milestogo/ergo_reform/reform2-keyboard-pcb/reform2-keyboard-backlight.kicad_sch

## KiCad design reform2-keyboard-pcb/reform2-keyboard-backlight.kicad_sch (2022-06-05)

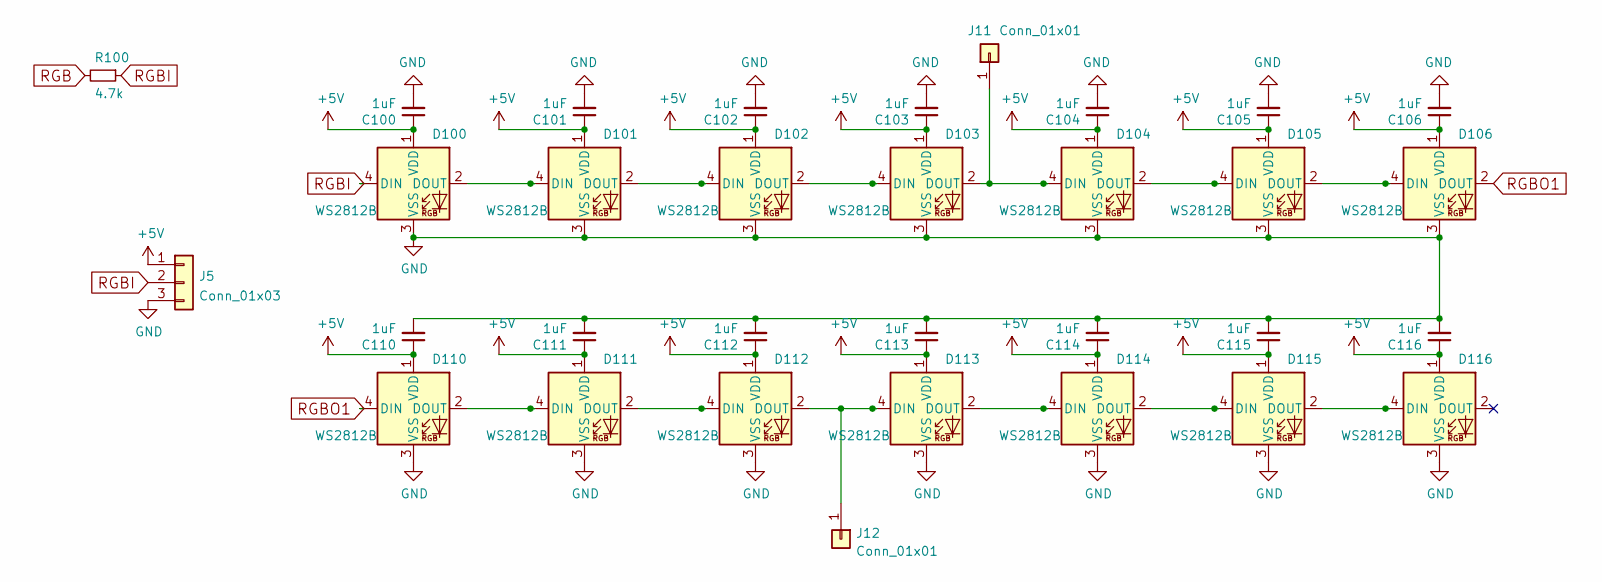
[picture p25: schematic reform2-keyboard-backlight.kicad_sch]

Parts:
C100, C101, C102, C103, C104, C105, C106, C110, C111, C112, C113, C114, C115, C116: 1uF; C_0805_2012Metric_Pad1.18x1.45mm_HandSolder
D100, D101, D102, D103, D104, D105, D106, D110, D111, D112, D113, D114, D115, D116: WS2812B; SK6812-MINI-E
J5: Conn_01x03; PinHeader_1x03_P2.54mm_Vertical
J11, J12: Conn_01x01; PinHeader_1x01_P2.00mm_Vertical
R100: 4.7k; R_0805_2012Metric_Pad1.20x1.40mm_HandSolder

Connections:
+5V: C100.1, C101.1, C102.1, C103.1, C104.1, C105.1, C106.1, C110.1, C111.1, C112.1, C113.1, C114.1, C115.1, C116.1, D100.1 (VDD), D101.1 (VDD), D102.1 (VDD), D103.1 (VDD), D104.1 (VDD), D105.1 (VDD), D106.1 (VDD), D110.1 (VDD), D111.1 (VDD), D112.1 (VDD), D113.1 (VDD), D114.1 (VDD), D115.1 (VDD), D116.1 (VDD), J5.1
GND: C100.2, C101.2, C102.2, C103.2, C104.2, C105.2, C106.2, C110.2, C111.2, C112.2, C113.2, C114.2, C115.2, C116.2, D100.3 (VSS), D101.3 (VSS), D102.3 (VSS), D103.3 (VSS), D104.3 (VSS), D105.3 (VSS), D106.3 (VSS), D110.3 (VSS), D111.3 (VSS), D112.3 (VSS), D113.3 (VSS), D114.3 (VSS), D115.3 (VSS), D116.3 (VSS), J5.3
unnamed: D100.2 (DOUT), D101.4 (DIN)
unnamed: D101.2 (DOUT), D102.4 (DIN)
unnamed: D102.2 (DOUT), D103.4 (DIN)
unnamed: D103.2 (DOUT), D104.4 (DIN), J11.1
unnamed: D104.2 (DOUT), D105.4 (DIN)
unnamed: D105.2 (DOUT), D106.4 (DIN)
unnamed: D110.2 (DOUT), D111.4 (DIN)
unnamed: D111.2 (DOUT), D112.4 (DIN)
unnamed: D112.2 (DOUT), D113.4 (DIN), J12.1
unnamed: D113.2 (DOUT), D114.4 (DIN)
unnamed: D114.2 (DOUT), D115.4 (DIN)
unnamed: D115.2 (DOUT), D116.4 (DIN)
RGB: R100.2
RGBI: D100.4 (DIN), J5.2, R100.1
RGBO1: D106.2 (DOUT), D110.4 (DIN)
