milestogo/ergo_reform/reform2-keyboard-pcb/reform2-keyboard.kicad_sch

## KiCad design reform2-keyboard-pcb/reform2-keyboard.kicad_sch (2022-06-05)

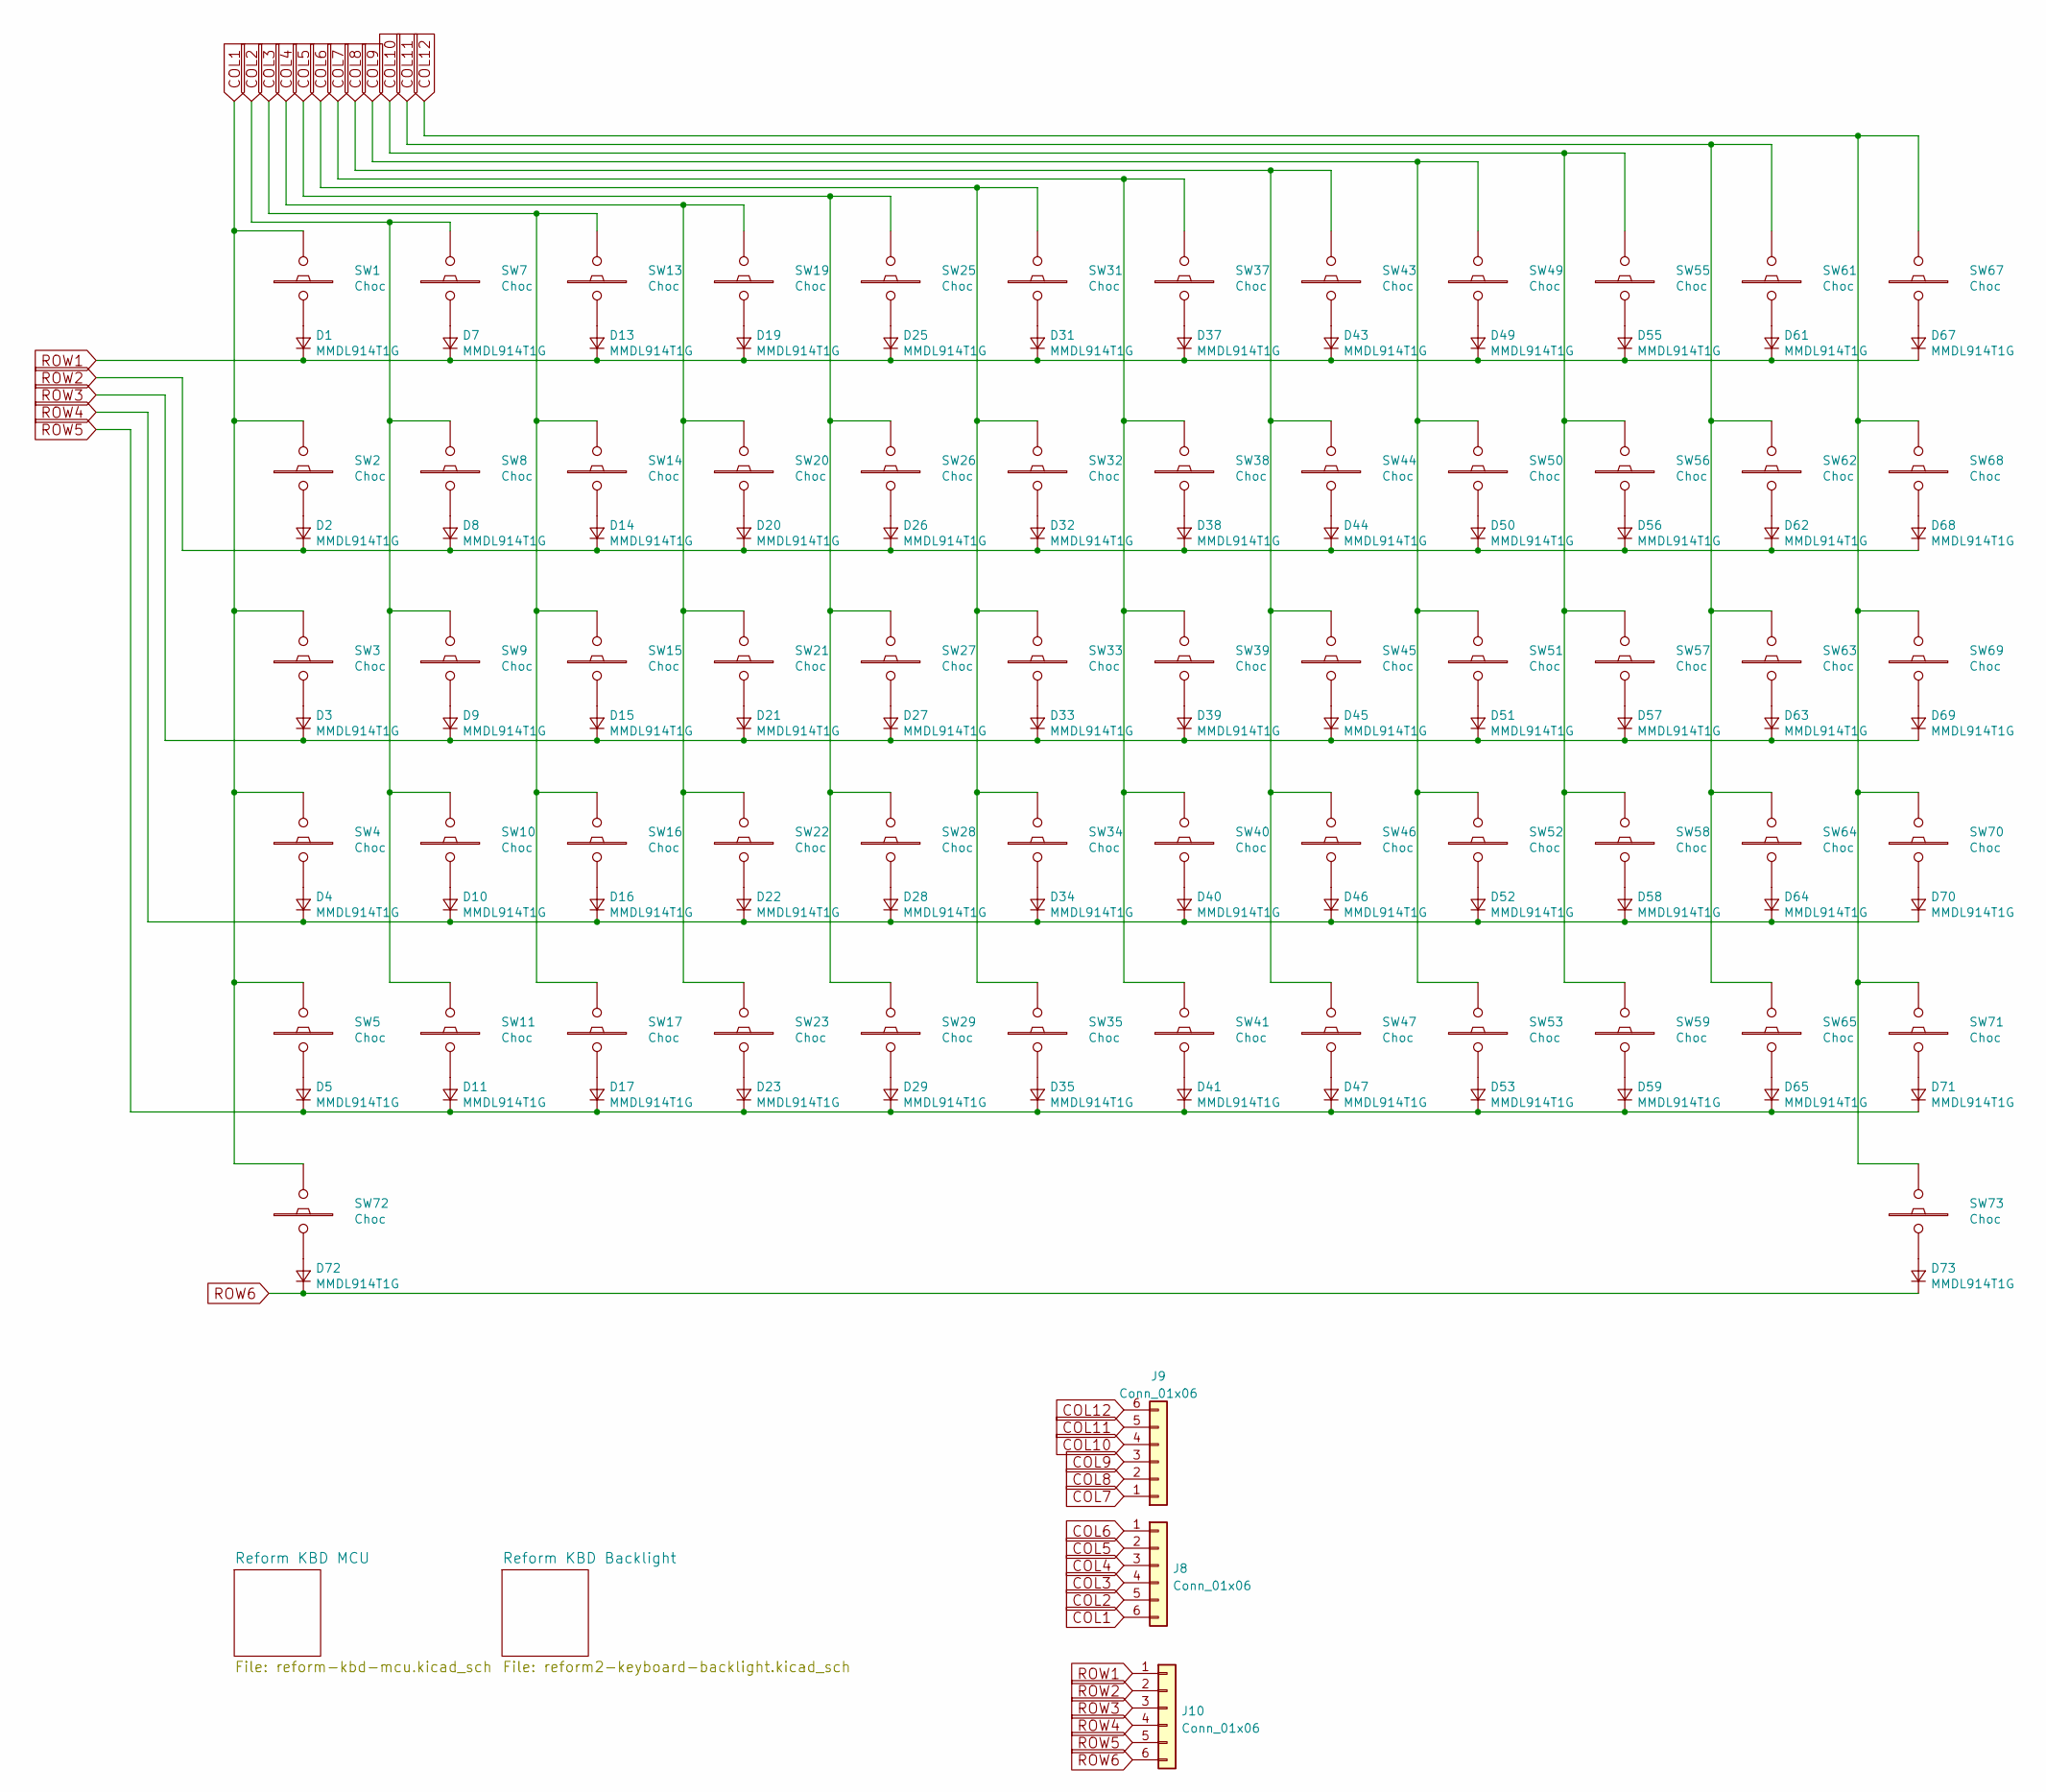
[picture p26: schematic reform2-keyboard.kicad_sch]

Parts:
D1, D2, D3, D4, D5, D7, D8, D9, D10, D11, D13, D14, D15, D16, D17, D19, D20, D21, D22, D23, D25, D26, D27, D28, D29, D31, D32, D33, D34, D35, D37, D38, D39, D40, D41, D43, D44, D45, D46, D47, D49, D50, D51, D52, D53, D55, D56, D57, D58, D59, D61, D62, D63, D64, D65, D67, D68, D69, D70, D71, D72, D73: MMDL914T1G; D_SOD-123
J8, J9, J10: Conn_01x06; PinHeader_1x06_P2.54mm_Vertical
SW1, SW7, SW13, SW27, SW29, SW35, SW41, SW45, SW47, SW55, SW61, SW67, SW72, SW73: Choc; PG1350
SW2, SW3, SW4, SW5, SW8, SW9, SW10, SW11, SW14, SW15, SW16, SW17, SW19, SW20, SW21, SW22, SW23, SW25, SW26, SW28, SW31, SW32, SW33, SW34, SW37, SW38, SW39, SW40, SW43, SW44, SW46, SW49, SW50, SW51, SW52, SW53, SW56, SW57, SW58, SW59, SW62, SW63, SW64, SW65, SW68, SW69, SW70, SW71: Choc; PG1350_optional-socket

Connections:
COL1: J8.6, SW1.1, SW2.1, SW3.1, SW4.1, SW5.1, SW72.1
COL2: J8.5, SW7.1, SW8.1, SW9.1, SW10.1, SW11.1
COL3: J8.4, SW13.1, SW14.1, SW15.1, SW16.1, SW17.1
COL4: J8.3, SW19.1, SW20.1, SW21.1, SW22.1, SW23.1
COL5: J8.2, SW25.1, SW26.1, SW27.1, SW28.1, SW29.1
COL6: J8.1, SW31.1, SW32.1, SW33.1, SW34.1, SW35.1
COL7: J9.1, SW37.1, SW38.1, SW39.1, SW40.1, SW41.1
COL8: J9.2, SW43.1, SW44.1, SW45.1, SW46.1, SW47.1
COL9: J9.3, SW49.1, SW50.1, SW51.1, SW52.1, SW53.1
COL10: J9.4, SW55.1, SW56.1, SW57.1, SW58.1, SW59.1
COL11: J9.5, SW61.1, SW62.1, SW63.1, SW64.1, SW65.1
COL12: J9.6, SW67.1, SW68.1, SW69.1, SW70.1, SW71.1, SW73.1
unnamed: D1.2 (A), SW1.2
unnamed: D2.2 (A), SW2.2
unnamed: D3.2 (A), SW3.2
unnamed: D4.2 (A), SW4.2
unnamed: D5.2 (A), SW5.2
unnamed: D7.2 (A), SW7.2
unnamed: D8.2 (A), SW8.2
unnamed: D9.2 (A), SW9.2
unnamed: D10.2 (A), SW10.2
unnamed: D11.2 (A), SW11.2
unnamed: D13.2 (A), SW13.2
unnamed: D14.2 (A), SW14.2
unnamed: D15.2 (A), SW15.2
unnamed: D16.2 (A), SW16.2
unnamed: D17.2 (A), SW17.2
unnamed: D19.2 (A), SW19.2
unnamed: D20.2 (A), SW20.2
unnamed: D21.2 (A), SW21.2
unnamed: D22.2 (A), SW22.2
unnamed: D23.2 (A), SW23.2
unnamed: D25.2 (A), SW25.2
unnamed: D26.2 (A), SW26.2
unnamed: D27.2 (A), SW27.2
unnamed: D28.2 (A), SW28.2
unnamed: D29.2 (A), SW29.2
unnamed: D31.2 (A), SW31.2
unnamed: D32.2 (A), SW32.2
unnamed: D33.2 (A), SW33.2
unnamed: D34.2 (A), SW34.2
unnamed: D35.2 (A), SW35.2
unnamed: D37.2 (A), SW37.2
unnamed: D38.2 (A), SW38.2
unnamed: D39.2 (A), SW39.2
unnamed: D40.2 (A), SW40.2
unnamed: D41.2 (A), SW41.2
unnamed: D43.2 (A), SW43.2
unnamed: D44.2 (A), SW44.2
unnamed: D45.2 (A), SW45.2
unnamed: D46.2 (A), SW46.2
unnamed: D47.2 (A), SW47.2
unnamed: D49.2 (A), SW49.2
unnamed: D50.2 (A), SW50.2
unnamed: D51.2 (A), SW51.2
unnamed: D52.2 (A), SW52.2
unnamed: D53.2 (A), SW53.2
unnamed: D55.2 (A), SW55.2
unnamed: D56.2 (A), SW56.2
unnamed: D57.2 (A), SW57.2
unnamed: D58.2 (A), SW58.2
unnamed: D59.2 (A), SW59.2
unnamed: D61.2 (A), SW61.2
unnamed: D62.2 (A), SW62.2
unnamed: D63.2 (A), SW63.2
unnamed: D64.2 (A), SW64.2
unnamed: D65.2 (A), SW65.2
unnamed: D67.2 (A), SW67.2
unnamed: D68.2 (A), SW68.2
unnamed: D69.2 (A), SW69.2
unnamed: D70.2 (A), SW70.2
unnamed: D71.2 (A), SW71.2
unnamed: D72.2 (A), SW72.2
unnamed: D73.2 (A), SW73.2
ROW1: D1.1 (K), D7.1 (K), D13.1 (K), D19.1 (K), D25.1 (K), D31.1 (K), D37.1 (K), D43.1 (K), D49.1 (K), D55.1 (K), D61.1 (K), D67.1 (K), J10.1
ROW2: D2.1 (K), D8.1 (K), D14.1 (K), D20.1 (K), D26.1 (K), D32.1 (K), D38.1 (K), D44.1 (K), D50.1 (K), D56.1 (K), D62.1 (K), D68.1 (K), J10.2
ROW3: D3.1 (K), D9.1 (K), D15.1 (K), D21.1 (K), D27.1 (K), D33.1 (K), D39.1 (K), D45.1 (K), D51.1 (K), D57.1 (K), D63.1 (K), D69.1 (K), J10.3
ROW4: D4.1 (K), D10.1 (K), D16.1 (K), D22.1 (K), D28.1 (K), D34.1 (K), D40.1 (K), D46.1 (K), D52.1 (K), D58.1 (K), D64.1 (K), D70.1 (K), J10.4
ROW5: D5.1 (K), D11.1 (K), D17.1 (K), D23.1 (K), D29.1 (K), D35.1 (K), D41.1 (K), D47.1 (K), D53.1 (K), D59.1 (K), D65.1 (K), D71.1 (K), J10.5
ROW6: D72.1 (K), D73.1 (K), J10.6
