milestogo/ergo_reform/reform2-keyboard-pcb/reform-kbd-mcu.kicad_sch

## KiCad design reform2-keyboard-pcb/reform-kbd-mcu.kicad_sch (2022-06-05)

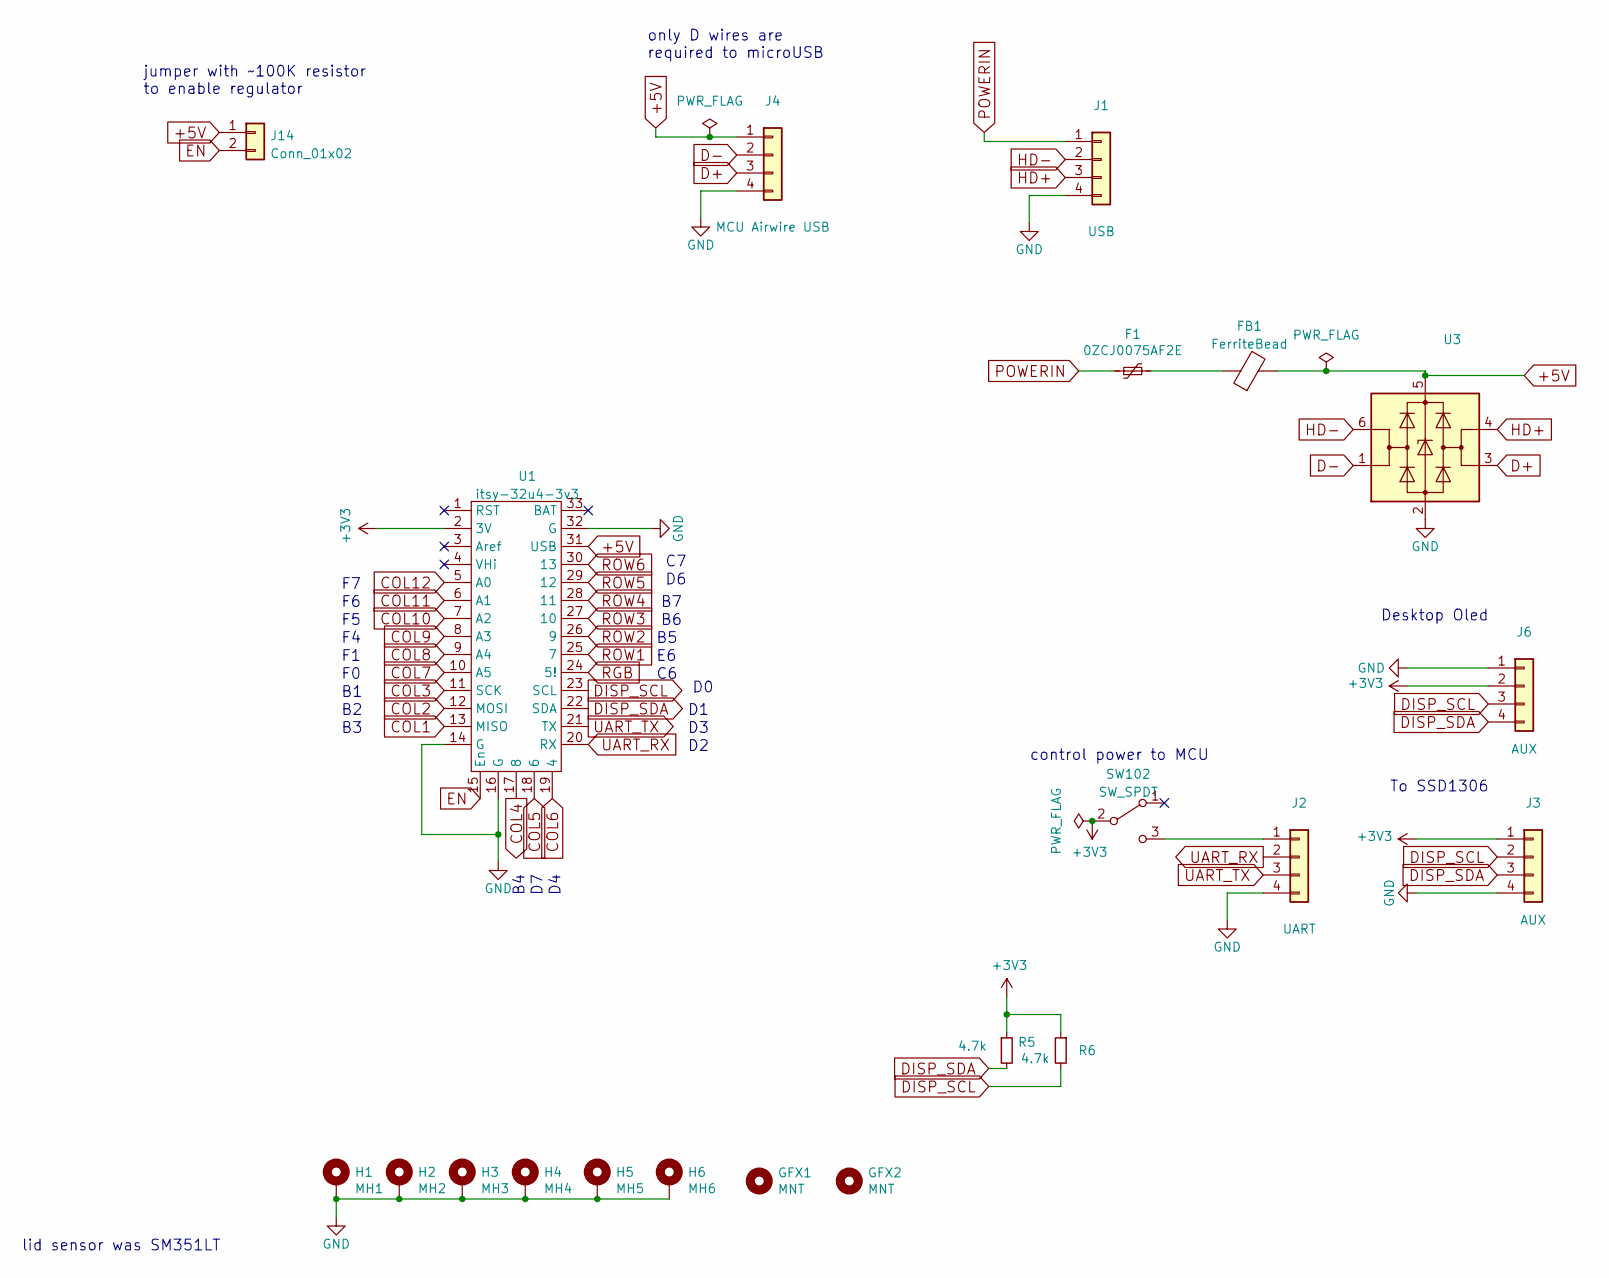
[picture p27: schematic reform-kbd-mcu.kicad_sch]

Parts:
F1: 0ZCJ0075AF2E; R_1206_3216Metric; LCSC C70082
FB1: FerriteBead; R_0805_2012Metric_Pad1.20x1.40mm_HandSolder
GFX1, GFX2: MNT; mnt-remix-reform
H1: MH1; MountingHole_2.2mm_M2_Pad
H2: MH2; MountingHole_2.2mm_M2_Pad
H3: MH3; MountingHole_2.2mm_M2_Pad
H4: MH4; MountingHole_2.2mm_M2_Pad
H5: MH5; MountingHole_2.2mm_M2_Pad
H6: MH6; MountingHole_2.2mm_M2_Pad
J1: USB; JST_PH_S4B-PH-SM4-TB_1x04-1MP_P2.00mm_Horizontal
J2: UART; JST_PH_S4B-PH-SM4-TB_1x04-1MP_P2.00mm_Horizontal
J3: AUX; Molex_200528-0040_1x04-1MP_P1.00mm_Horizontal
J4: MCU Airwire USB; PinHeader_1x04_P2.54mm_Vertical
J6: AUX; PinHeader_1x04_P2.54mm_Vertical
J14: Conn_01x02; PinHeader_1x02_P2.54mm_Vertical
R5, R6: 4.7k; R_0805_2012Metric_Pad1.20x1.40mm_HandSolder
SW102: SW_SPDT; SW_Push_1P2T_Vertical_E-Switch_800UDP8P1A1M6
U1: itsy-32u4-3v3; ItsyBitsy-32u4
U3: SOT-23-6_Handsoldering; LCSC C2687116

Connections:
+3V3: J3.1, J6.2, R5.1, R6.1, SW102.2 (B), U1.2 (3V)
+5V: FB1.2, J4.1, J14.1, U1.31 (USB), U3.5 (VBUS)
COL1: U1.13 (MISO)
COL2: U1.12 (MOSI)
COL3: U1.11 (SCK)
COL4: U1.17 (8)
COL5: U1.18 (6)
COL6: U1.19 (4)
COL7: U1.10 (A5)
COL8: U1.9 (A4)
COL9: U1.8 (A3)
COL10: U1.7 (A2)
COL11: U1.6 (A1)
COL12: U1.5 (A0)
D+: J4.3, U3.3 (I/O2)
D-: J4.2, U3.1 (I/O1)
DISP_SCL: J3.2, J6.3, R6.2, U1.23 (SCL)
DISP_SDA: J3.3, J6.4, R5.2, U1.22 (SDA)
EN: J14.2, U1.15 (En)
GND: H1.1, H2.1, H3.1, H4.1, H5.1, H6.1, J1.4, J2.4, J3.4, J4.4, J6.1, U1.14 (G), U1.16 (G), U1.32 (G), U3.2 (GND)
HD+: J1.3, U3.4 (I/O2)
HD-: J1.2, U3.6 (I/O1)
unnamed: F1.2, FB1.1
unnamed: J2.1, SW102.3 (C)
POWERIN: F1.1, J1.1
RGB: U1.24 (5!)
ROW1: U1.25 (7)
ROW2: U1.26 (9)
ROW3: U1.27 (10)
ROW4: U1.28 (11)
ROW5: U1.29 (12)
ROW6: U1.30 (13)
UART_RX: J2.2, U1.20 (RX)
UART_TX: J2.3, U1.21 (TX)

Notes on the sheet:
To SSD1306
jumper with ~100K resistor to enable regulator
only D wires are required to microUSB
Desktop Oled
control power to MCU
lid sensor was SM351LT
